hmcbiophotonics/3d-Printed-Microscopes/simulations/figures/input_amplitude_figure.png

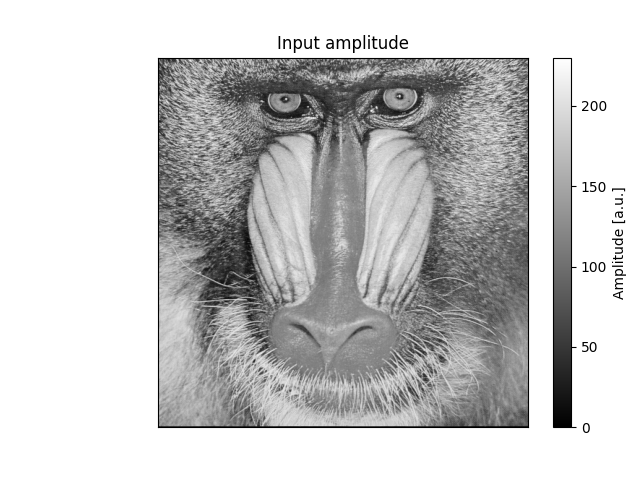
simulations/figures/input_amplitude_figure.png
