hmcbiophotonics/3d-Printed-Microscopes/simulations/figures/landscape_gray.png

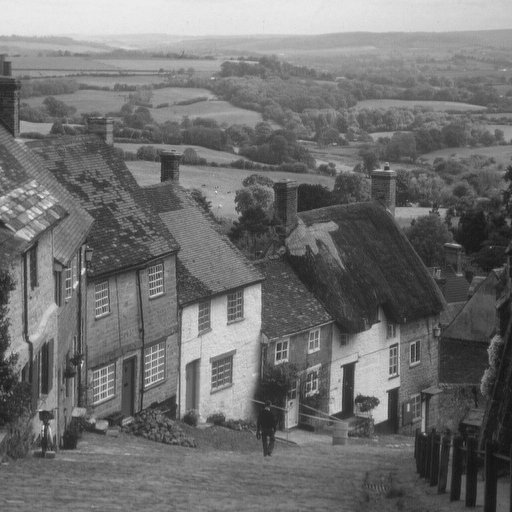
simulations/figures/landscape_gray.png
