hmcbiophotonics/3d-Printed-Microscopes/simulations/figures/monkey_gray.png

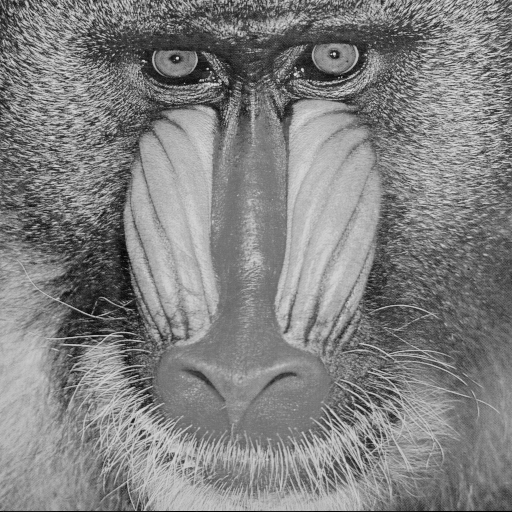
simulations/figures/monkey_gray.png
